StdBx/Series100/Series100 Examples/StdBx Proto Board w UNO(ALPHA).sch

## EAGLE design Series100 Examples/StdBx Proto Board w UNO(ALPHA).sch (2014-12-12)

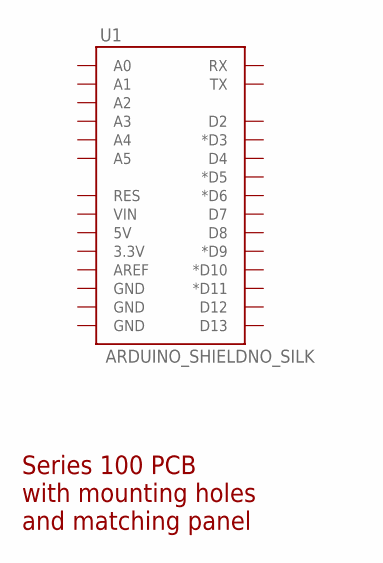
[picture p6: schematic StdBx Proto Board w UNO(ALPHA).sch]

Parts:
U1: ARDUINO_SHIELDNO_SILK; DUEMILANOVE_VIAS
U$1: SERIES_100"; SERIES_100
